wmurphy41/LIDAR-Scanner/code/processing/LidarScanner.pde

// LidarScanner.pde Processing sketch
// http://www.qcontinuum.org/lidar

// Load sketch into Processing, available from:
// https://processing.org/

// This sketch accepts XYZ coordinates from Arduino LIDAR scanner
// and displays them graphically as a 3D point cloud that you can
// pan, zoom, and rotate using keyboard.

import processing.serial.*;

Serial serial;
int serialPortNumber = 0;
float angle = 6.5f;
float angleIncrement = 0;
float xOffset = 3.0;
float xOffsetIncrement = 0;
float yOffset = 152.0f;
float yOffsetIncrement = 0;
float scale = 2.6f;
float scaleIncrement = 0;
ArrayList<PVector> vectors;
int lastPointIndex = 0;
int lastPointCount = 0;

void setup() {
  size(800, 600, P3D);
  colorMode(RGB, 255, 255, 255);
  noSmooth();
  vectors = new ArrayList<PVector>();
  String[] serialPorts = Serial.list();
  if (serialPorts.length == 0) {
    println("No ports found!") ;
  }   
  String serialPort = serialPorts[serialPortNumber];
  println("Using serial port \"" + serialPort + "\"");
  println("To use a different serial port, change serialPortNumber:");
  printArray(serialPorts);
  serial = new Serial(this, serialPort, 9600); 
  
  delay(1000) ;
}
void draw() {
  String input = serial.readStringUntil(10);
  if (input != null) {
    println(input) ;
    String[] components = split(input, ' ');
    if (components.length == 3) {
      vectors.add(new PVector(float(components[0]), float(components[1]), float(components[2])));
    }
  }
  background(0);
  translate(width/2, height/2, -50);
  rotateY(angle);
  int size = vectors.size();
  for (int index = 0; index < size; index++) {
    PVector v = vectors.get(index);
    if (index == size - 1) {
      // draw red line to show recently added LIDAR scan point
      if (index == lastPointIndex) {
        lastPointCount++;
      } else {
        lastPointIndex = index;
        lastPointCount = 0;
      }
      if (lastPointCount < 10) {
        stroke(255, 0, 0);
        line(xOffset, yOffset, 0, v.x * scale + xOffset, -v.z * scale + yOffset, -v.y * scale);
      }
    }
    stroke(255, 255, 255);
    point(v.x * scale + xOffset, -v.z * scale + yOffset, -v.y * scale);
  }
  angle += angleIncrement;
  xOffset += xOffsetIncrement;
  yOffset += yOffsetIncrement;
  scale += scaleIncrement;
}

void keyPressed() {
  if (key == 'q') {
    // zoom in
    scaleIncrement = 0.02f;
  } else if (key == 'z') {
    // zoom out
    scaleIncrement = -0.02f;
  } else if (key == 'a') {
    // move left
    xOffsetIncrement = -1f;
  } else if (key == 'd') {
    // move right
    xOffsetIncrement = 1f;
  } else if (key == 'w') {
    // move up
    yOffsetIncrement = -1f;
  } else if (key == 's') {
    // move down
    yOffsetIncrement = 1f;
  } else if (key =='x') {
    // erase all points
    vectors.clear();
    
  } else if (key == CODED) {
    if (keyCode == LEFT) {
      // rotate left
      angleIncrement = -0.015f;
    } else if (keyCode == RIGHT) {
      // rotate right
      angleIncrement = 0.015f;
    }
  } else 
    serial.write(key) ;
}

void keyReleased() {
  if (key == 'q') {
    scaleIncrement = 0f;
  } else if (key == 'z') {
    scaleIncrement = 0f;
  } else if (key == 'a') {
    xOffsetIncrement = 0f;
  } else if (key == 'd') {
    xOffsetIncrement = 0f;
  } else if (key == 'w') {
    yOffsetIncrement = 0f;
  } else if (key == 's') {
    yOffsetIncrement = 0f;
  } else if (key == CODED) {
    if (keyCode == LEFT) {
      angleIncrement = 0f;
    } else if (keyCode == RIGHT) {
      angleIncrement = 0f;
    }
  }
}
