wmurphy41/LIDAR-Scanner/code/arduino/turntable_unit_test/pins.h

#ifndef PINS_H
#define PINS_H


//Define the pin connections for the Turntable
const int DIR_PIN = 10 ;
const int STEP_PIN = 11 ;
const int ENABLE_PIN =  12 ;       // Enable pin for stepper


#endif //PINS_H
